dtyulman/tddcs/single-stage/Solidworks/Isolator.sldprt

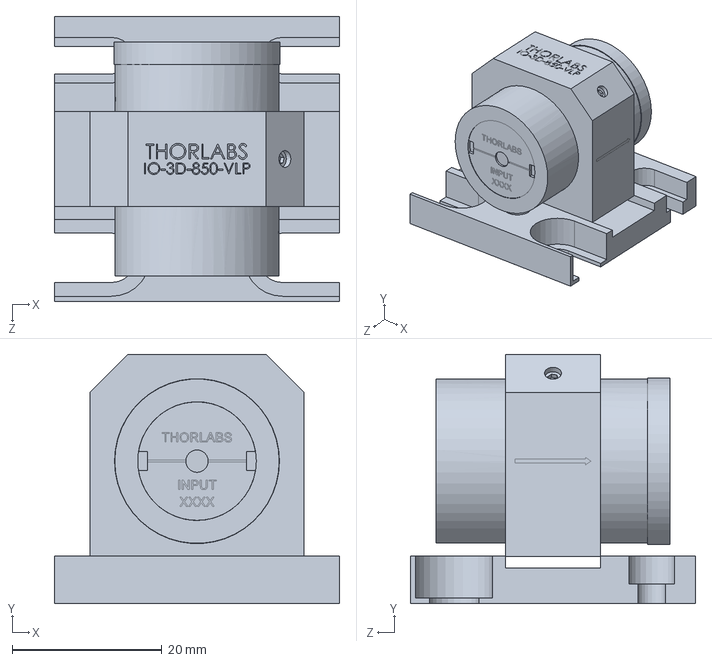
[picture p42: CAD file, 2017-01-31]
single-stage/Solidworks/Isolator.sldprt
38.1 x 33.4 x 38.1 mm
