dtyulman/tddcs/single-stage/Solidworks/Rod_ER4.SLDPRT

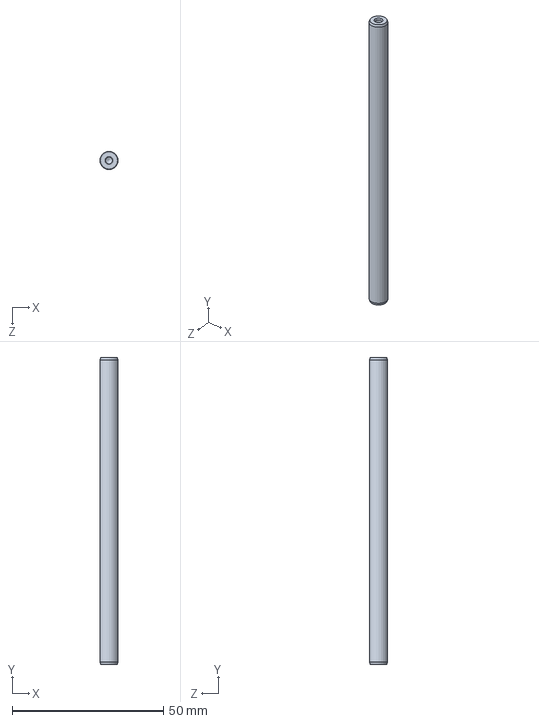
[picture p43: CAD file, 2017-01-31]
single-stage/Solidworks/Rod_ER4.SLDPRT
5.99 x 101.6 x 5.99 mm
