dtyulman/tddcs/single-stage/Solidworks/CagePlate30mm_CP02.sldprt

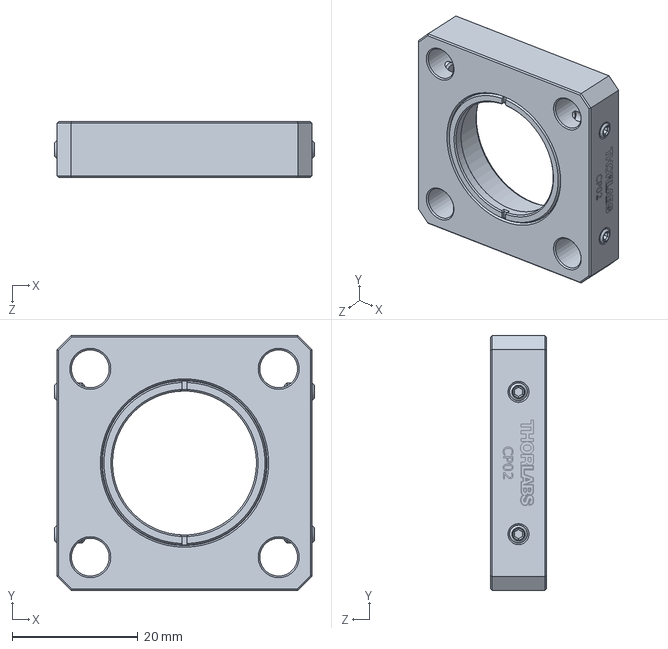
[picture p44: CAD file, 2017-01-31]
single-stage/Solidworks/CagePlate30mm_CP02.sldprt
41.4 x 40.6 x 8.89 mm
