dtyulman/tddcs/single-stage/Solidworks/XYTranslator_CXY01.sldprt

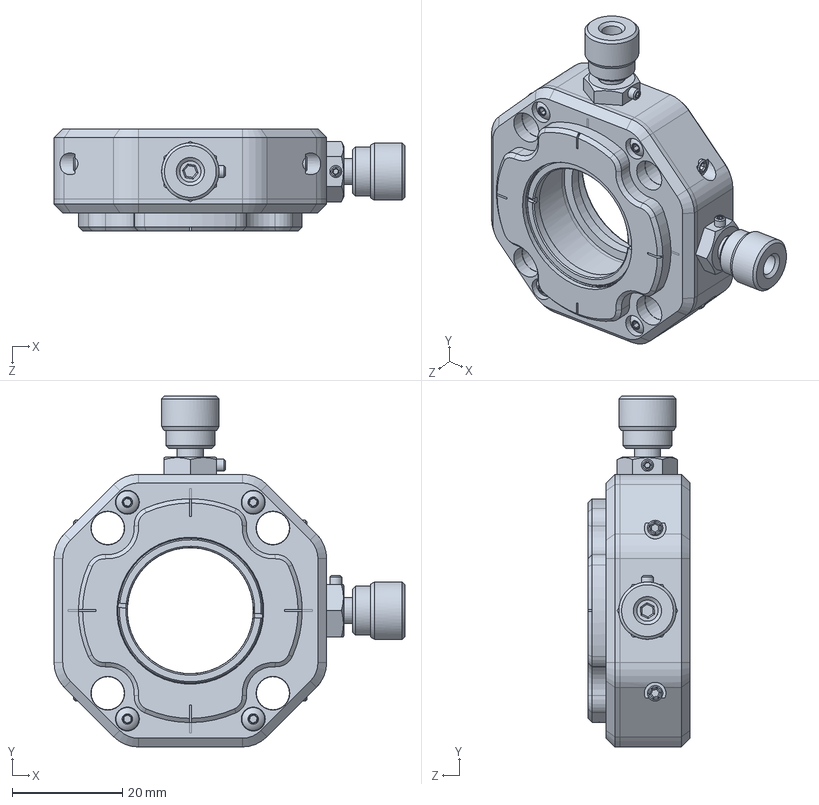
[picture p45: CAD file, 2017-01-31]
single-stage/Solidworks/XYTranslator_CXY01.sldprt
63.8 x 63.7 x 18.6 mm
